jdburgie/esp32-epaper-web/icon.h

#pragma once
// PROGMEM: keeps this ~23KB blob in flash instead of RAM (required on ESP8266,
// harmless/no-op on ESP32). Served via beginResponse_P, which reads it correctly.
const unsigned char webapp_icon_192_png[] PROGMEM = {
  0x89, 0x50, 0x4e, 0x47, 0x0d, 0x0a, 0x1a, 0x0a, 0x00, 0x00, 0x00, 0x0d,
  0x49, 0x48, 0x44, 0x52, 0x00, 0x00, 0x00, 0xc0, 0x00, 0x00, 0x00, 0xc0,
  0x08, 0x06, 0x00, 0x00, 0x00, 0x52, 0xdc, 0x6c, 0x07, 0x00, 0x00, 0x00,
  0x06, 0x62, 0x4b, 0x47, 0x44, 0x00, 0xff, 0x00, 0xff, 0x00, 0xff, 0xa0,
  0xbd, 0xa7, 0x93, 0x00, 0x00, 0x20, 0x00, 0x49, 0x44, 0x41, 0x54, 0x78,
  0x9c, 0xec, 0x9d, 0x77, 0x58, 0x54, 0xd7, 0xd6, 0x87, 0xdf, 0x33, 0x03,
  0x0c, 0xbd, 0x77, 0x29, 0x02, 0x4a, 0x11, 0x05, 0x2c, 0xa8, 0xd8, 0xc0,
  0x12, 0x63, 0xef, 0x2d, 0x6a, 0x12, 0xa3, 0x26, 0x26, 0x57, 0x53, 0x4c,
  0x6e, 0x6e, 0x6e, 0xda, 0x4d, 0xb9, 0xe9, 0xbd, 0x19, 0x13, 0x4d, 0x62,
  0x4c, 0xd1, 0x18, 0x8d, 0xbd, 0xf7, 0x0e, 0x56, 0x44, 0x41, 0x11, 0x45,
  0xa9, 0xd2, 0x7b, 0x67, 0x98, 0x39, 0xdf, 0x1f, 0x03, 0x23, 0x23, 0x03,
  0x0c, 0x30, 0xa0, 0xb9, 0x9f, 0xef, 0xf3, 0xe4, 0x89, 0x33, 0xb3, 0xcf,
  0x99, 0x0d, 0xec, 0x75, 0xf6, 0xde, 0x6b, 0xaf, 0xf5, 0x5b, 0x70, 0x9f,
  0xfb, 0xdc, 0xe7, 0x3e, 0xf7, 0xb9, 0xcf, 0x7d, 0xee, 0x73, 0x9f, 0xfb,
  0xdc, 0xe7, 0x3e, 0xf7, 0xb9, 0xcf, 0x7d, 0xee, 0x73, 0x9f, 0xfb, 0xdc,
  0xe7, 0x3e, 0xff, 0xd3, 0x08, 0x77, 0xbb, 0x03, 0xff, 0xeb, 0x84, 0x2d,
  0x9d, 0x6e, 0x52, 0x5a, 0x59, 0x6e, 0xdc, 0x9a, 0x6b, 0x8d, 0x14, 0x99,
  0xa5, 0xe7, 0x56, 0x9c, 0x93, 0xeb, 0xbb, 0x4f, 0xf7, 0xb9, 0x4d, 0xab,
  0x0d, 0xa0, 0xc7, 0x53, 0x63, 0x6d, 0x94, 0xd5, 0x52, 0x3b, 0x89, 0xa0,
  0xb0, 0x12, 0xc0, 0x54, 0x89, 0x68, 0x2c, 0x48, 0x04, 0x6b, 0xa5, 0x52,
  0x30, 0x91, 0x20, 0x1a, 0x03, 0x88, 0x02, 0x32, 0x01, 0x4c, 0x55, 0xdf,
  0x24, 0x0a, 0x4a, 0x51, 0xb0, 0xae, 0xf7, 0xc5, 0x16, 0xa2, 0x80, 0x01,
  0x80, 0x44, 0x89, 0x4c, 0x14, 0x54, 0xed, 0x04, 0x10, 0x44, 0xb0, 0xd6,
  0xfc, 0x36, 0xd1, 0x0a, 0x04, 0x89, 0xd6, 0x1f, 0x40, 0x10, 0x24, 0x22,
  0xa2, 0x55, 0xa3, 0x1d, 0x15, 0x91, 0x51, 0xd7, 0x07, 0xed, 0x98, 0x01,
  0x46, 0x3a, 0xfc, 0xc8, 0xff, 0x8b, 0x94, 0x03, 0x55, 0x4d, 0x7c, 0x5e,
  0x8c, 0x80, 0x42, 0xeb, 0x27, 0x22, 0x4a, 0xa0, 0xa8, 0xd1, 0x2b, 0x45,
  0xaa, 0x11, 0x28, 0xab, 0xf7, 0x8e, 0x02, 0x28, 0xae, 0x7f, 0x6f, 0xb1,
  0xf6, 0xde, 0x82, 0x52, 0xa8, 0x14, 0x05, 0xb1, 0x02, 0x40, 0x40, 0x54,
  0x0a, 0x08, 0xea, 0xfb, 0x2a, 0xa1, 0x44, 0x22, 0x52, 0x03, 0x80, 0x20,
  0x94, 0x29, 0x51, 0x56, 0x4a, 0x10, 0x8a, 0x44, 0x28, 0x97, 0x08, 0x92,
  0x4a, 0xb1, 0x46, 0x59, 0x28, 0xc8, 0xe5, 0x59, 0x17, 0x7f, 0xdd, 0x5b,
  0xff, 0xbb, 0x74, 0x46, 0x67, 0x03, 0x88, 0x78, 0x33, 0xc2, 0x20, 0x2f,
  0xdd, 0x74, 0xae, 0x88, 0xf0, 0x38, 0xd0, 0x03, 0xb0, 0x68, 0xcd, 0x17,
  0xde, 0xe7, 0x3e, 0xed, 0x82, 0x48, 0x1e, 0x02, 0xd1, 0x82, 0xc0, 0x8a,
  0x4b, 0x2b, 0x76, 0x6c, 0x00, 0x44, 0x5d, 0x2e, 0xd3, 0xd5, 0x00, 0x84,
  0xee, 0x8f, 0x8f, 0xdd, 0x06, 0x8c, 0x6d, 0x75, 0x07, 0xef, 0x73, 0x9f,
  0x0e, 0x42, 0x80, 0xb5, 0x97, 0x56, 0xee, 0x98, 0xad, 0x63, 0xdb, 0xe6,
  0xe9, 0xf1, 0xf8, 0xe8, 0xd1, 0x22, 0x92, 0x9d, 0x6d, 0xeb, 0xd6, 0x7d,
  0xee, 0xd3, 0x71, 0x08, 0x12, 0x31, 0xfc, 0xd2, 0xf7, 0x3b, 0x8f, 0x36,
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
};
unsigned int webapp_icon_192_png_len = 23062;
