jdburgie/esp32-epaper-web/logo.h

// Three Oak Woods acorn badge (vector).
// Source: oaklink/branding/company/threeoakwoods-badge.svg — served at /logo.svg
#pragma once
// PROGMEM: keeps this ~12KB blob in flash instead of RAM (required on ESP8266,
// harmless/no-op on ESP32). Served via beginResponse_P, which reads it correctly.
const char THREEOAKWOODS_BADGE_SVG[] PROGMEM = R"TOW(
<svg xmlns="http://www.w3.org/2000/svg" viewBox="0 0 262 262" width="262" height="262" role="img" aria-label="Three Oak Woods badge">
  <title>Three Oak Woods — acorn &amp; oak-leaf badge (vector)</title>
  <g transform="translate(0.000000,262.000000) scale(0.100000,-0.100000)"
fill="#2C654B" stroke="none">
<path d="M172 2495 c-65 -28 -62 31 -62 -1185 0 -1221 -3 -1157 64 -1185 53
-22 2219 -22 2272 0 67 28 64 -36 64 1185 0 1221 3 1157 -64 1185 -52 22
-2224 22 -2274 0z"/>
</g>
  <g transform="translate(0.000000,262.000000) scale(0.100000,-0.100000)"
fill="#F9E7DF" stroke="none">
<path d="M1394 2411 c-34 -16 -80 -45 -101 -65 -39 -35 -41 -36 -121 -34 -71
0 -87 -3 -127 -26 -25 -15 -56 -43 -68 -62 -15 -23 -27 -32 -37 -27 -8 4 -37
8 -65 10 -42 4 -57 -1 -96 -25 -55 -35 -79 -81 -79 -150 0 -52 -9 -62 -51 -62
-11 0 -31 -11 -45 -25 -22 -22 -25 -33 -23 -78 l3 -52 -89 1 -90 2 -11 57 c-6
31 -18 64 -26 72 -13 13 -17 11 -28 -17 -11 -27 -10 -37 13 -88 14 -31 35 -90
47 -129 12 -40 30 -84 41 -97 26 -33 24 -51 -17 -161 -74 -197 -88 -279 -59
-335 18 -35 70 -76 108 -85 32 -8 32 -10 11 -82 -26 -90 -3 -193 58 -259 48
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
<path d="M981 560 c0 -8 4 -22 9 -30 12 -18 12 -2 0 25 -6 13 -9 15 -9 5z"/>
<path d="M1004 1354 c3 -8 6 -18 6 -20 0 -2 5 -4 10 -4 16 0 11 27 -6 34 -12
5 -15 2 -10 -10z"/>
<path d="M952 1352 c-7 -5 -22 -25 -33 -46 -16 -30 -17 -40 -7 -59 l12 -22 6
25 c6 24 6 24 17 5 10 -17 11 -12 10 30 -2 43 1 50 16 49 10 -1 16 3 14 9 -5
15 -19 18 -35 9z"/>
<path d="M1982 1089 c2 -7 24 -17 49 -21 60 -11 74 -3 21 11 -24 7 -50 15 -59
18 -11 4 -14 2 -11 -8z"/>
<path d="M1470 1051 c0 -11 5 -23 10 -26 6 -3 10 3 10 14 0 11 -4 23 -10 26
-5 3 -10 -3 -10 -14z"/>
<path d="M1572 1010 c0 -14 2 -19 5 -12 2 6 2 18 0 25 -3 6 -5 1 -5 -13z"/>
</g>
</svg>

)TOW";
